dechielmobiel/environment-sensing/pcb files/pictures/20221101_161000 (1).jpg

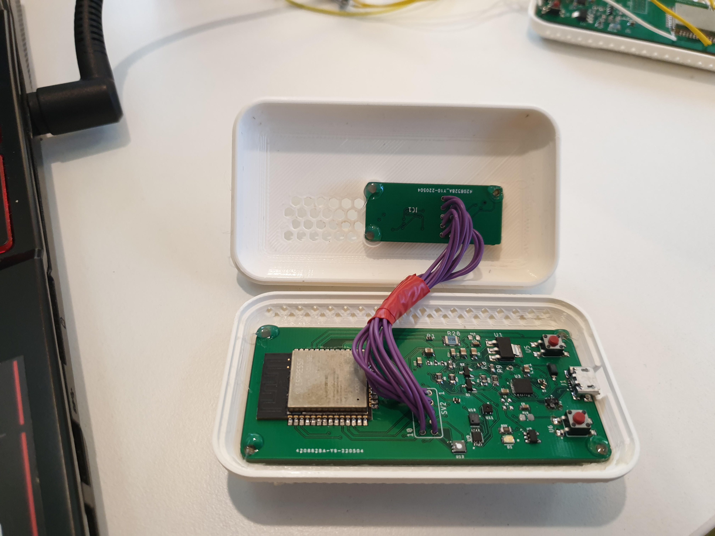
pcb files/pictures/20221101_161000 (1).jpg
